Radacon/ESP_Remote_Start/Images/PXL_20210329_001821744.jpg

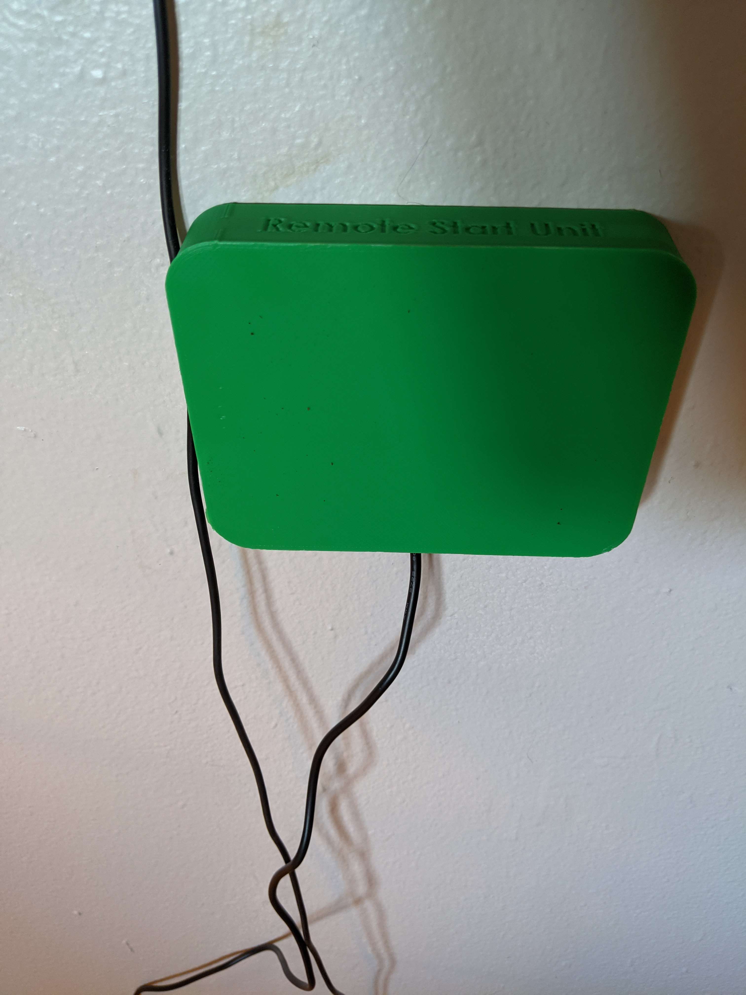
Images/PXL_20210329_001821744.jpg
