Radacon/ESP_Remote_Start/Images/PXL_20210329_001831299.jpg

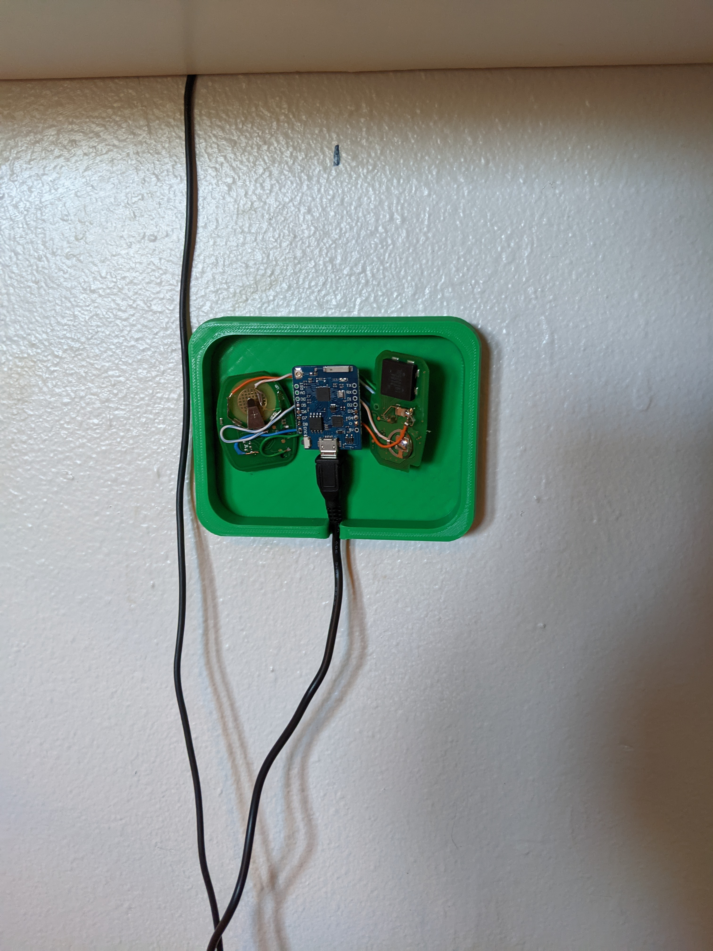
Images/PXL_20210329_001831299.jpg
