Radacon/ESP_Remote_Start/Images/PXL_20210329_001841422.jpg

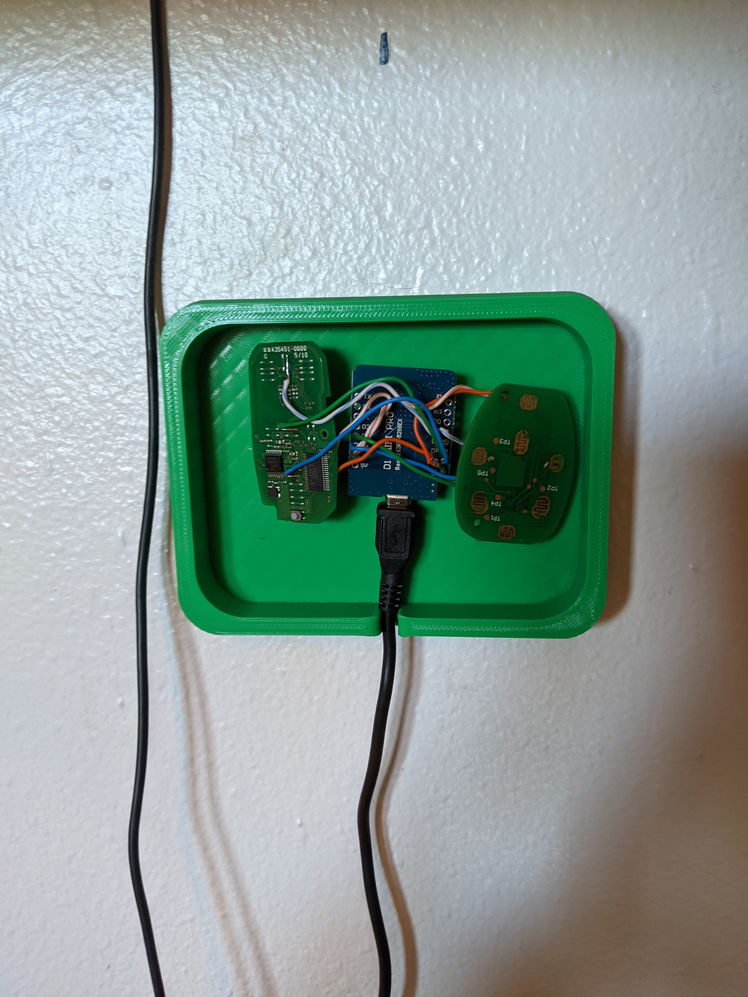
Images/PXL_20210329_001841422.jpg
