Radacon/ESP_Remote_Start/Images/PXL_20210329_001851826.jpg

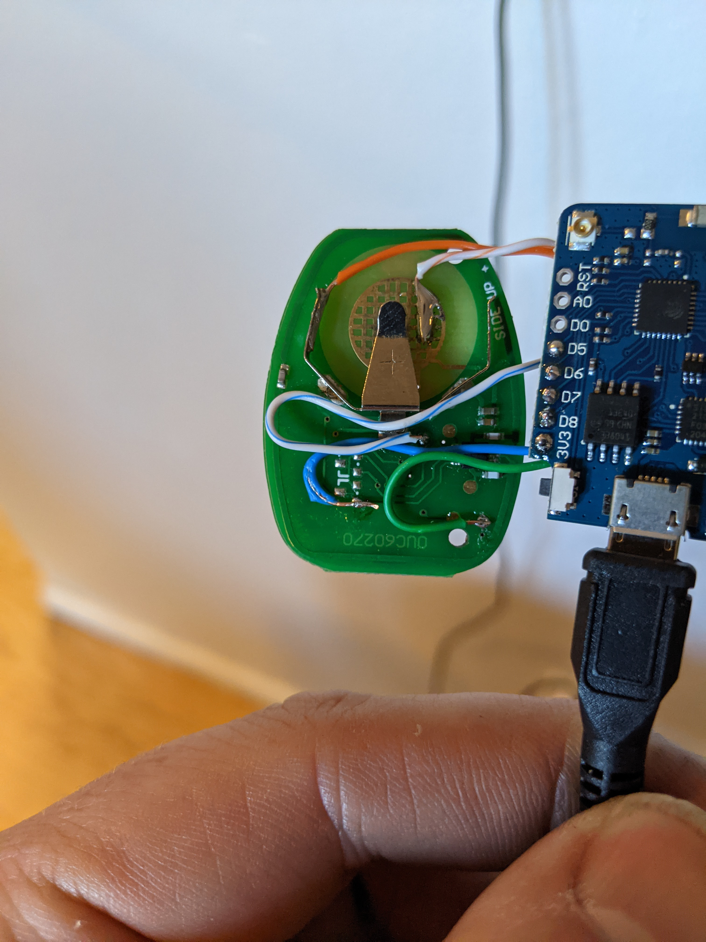
Images/PXL_20210329_001851826.jpg
